apirek/digimatic/schematics/Digimatic USB Adaptor.kicad_sch

## KiCad design schematics/Digimatic USB Adaptor.kicad_sch (2024-03-31)

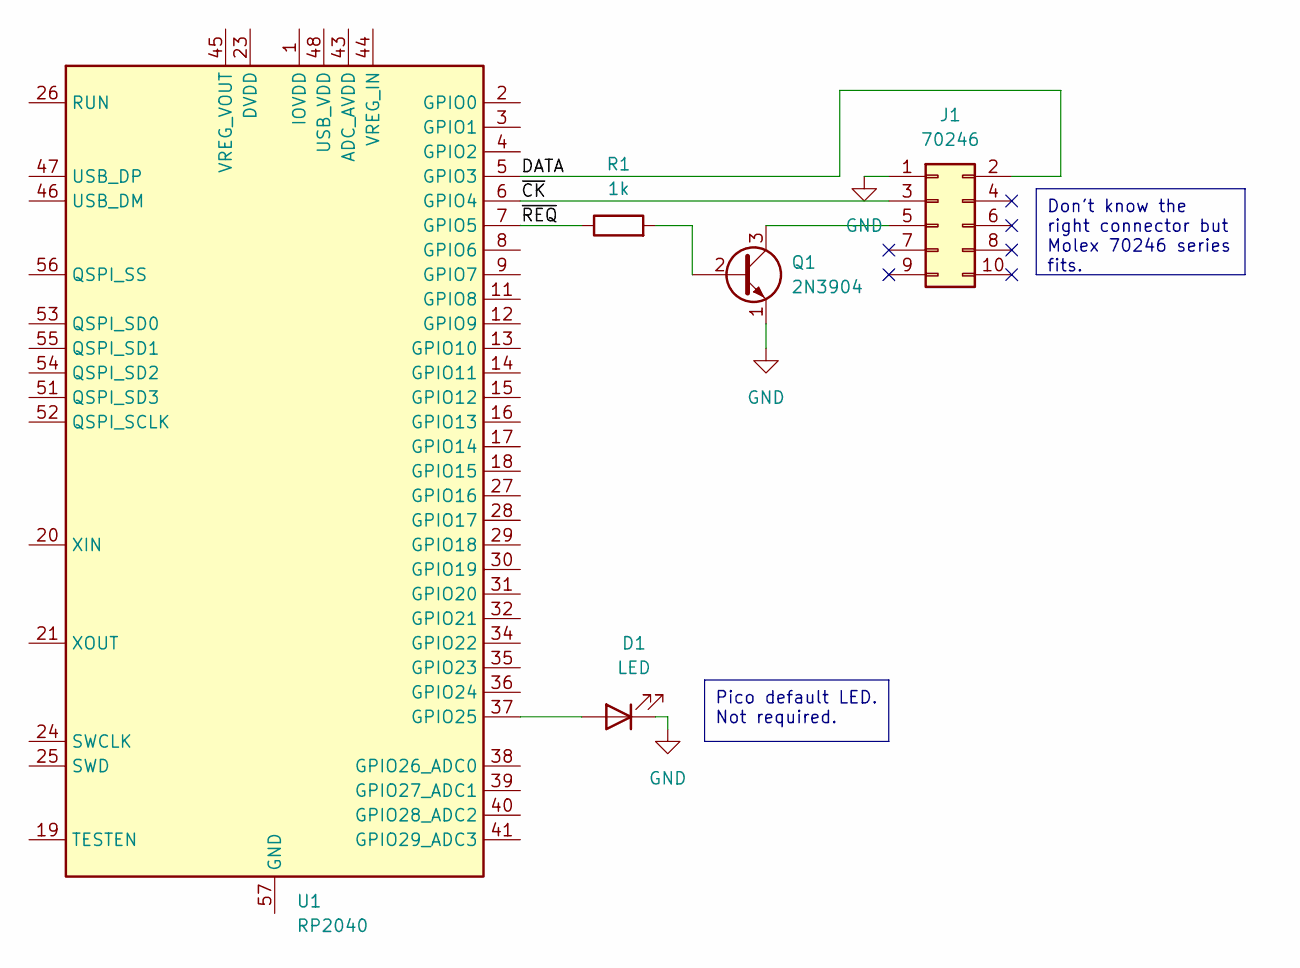
[picture p2: schematic Digimatic USB Adaptor.kicad_sch]

Parts:
D1: LED
J1: 70246
Q1: 2N3904; TO-92_Inline
R1: 1k
U1: RP2040; QFN-56-1EP_7x7mm_P0.4mm_EP3.2x3.2mm

Connections:
DATA: J1.2, U1.5 (GPIO3)
GND: D1.1 (K), J1.1, Q1.1 (E)
unnamed: D1.2 (A), U1.37 (GPIO25)
unnamed: J1.5, Q1.3 (C)
unnamed: Q1.2 (B), R1.2
unnamed: U1.1 (IOVDD), U1.10 (IOVDD), U1.22 (IOVDD), U1.33 (IOVDD), U1.42 (IOVDD), U1.49 (IOVDD)
unnamed: U1.23 (DVDD), U1.50 (DVDD)
~CK: J1.3, U1.6 (GPIO4)
~REQ: R1.1, U1.7 (GPIO5)

Notes on the sheet:
Pico default LED. Not required.
Don't know the right connector but Molex 70246 series fits.
